evanorsouw/panelclock/doc/images/pcb_back.jpg

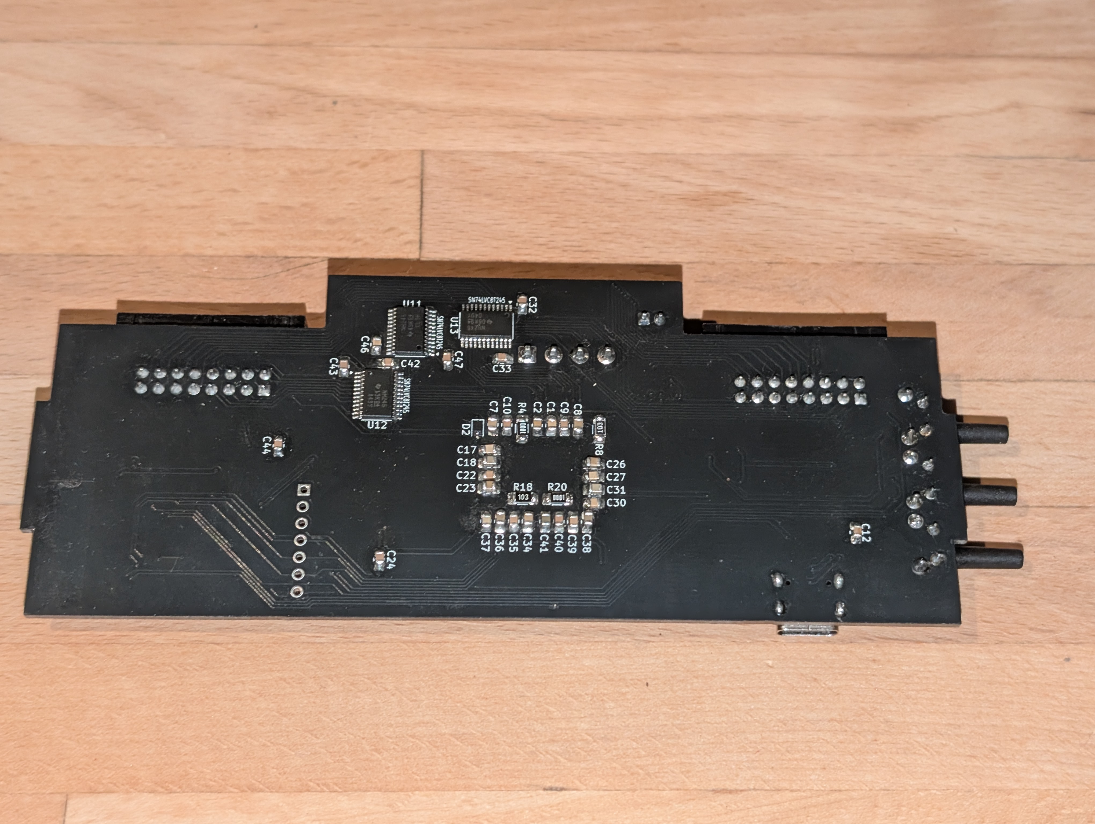
doc/images/pcb_back.jpg
