evanorsouw/panelclock/doc/images/parts_.jpg

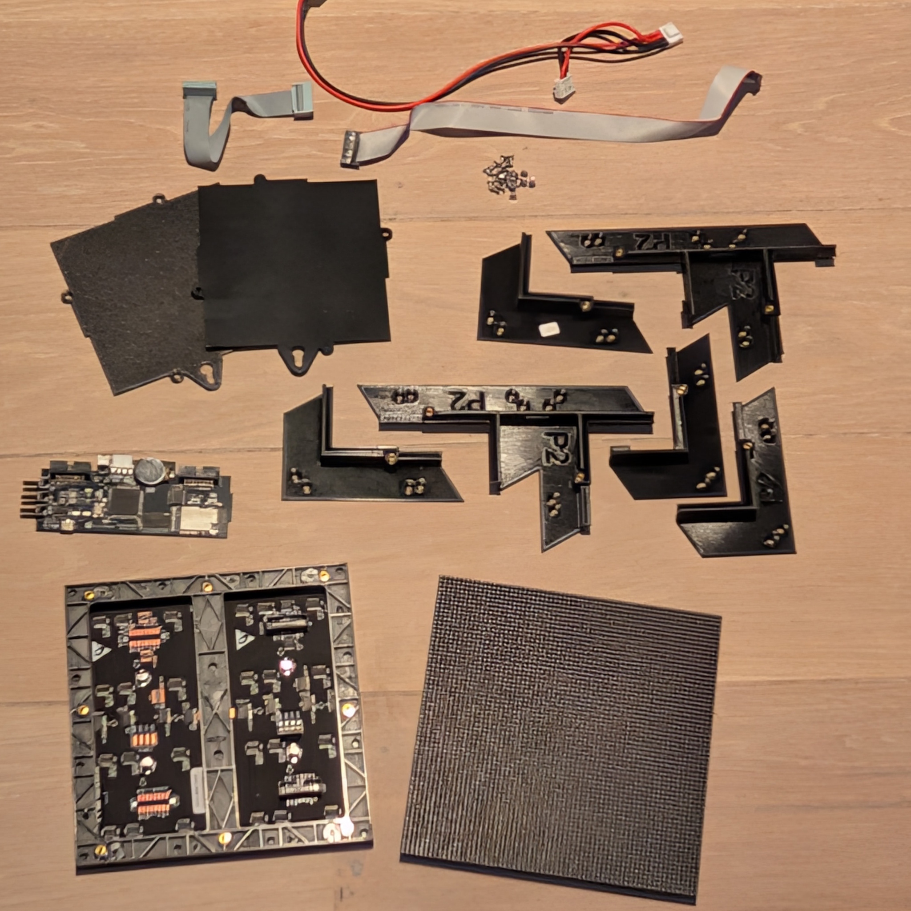
doc/images/parts_.jpg
