evanorsouw/panelclock/doc/images/partly_assembled.jpg

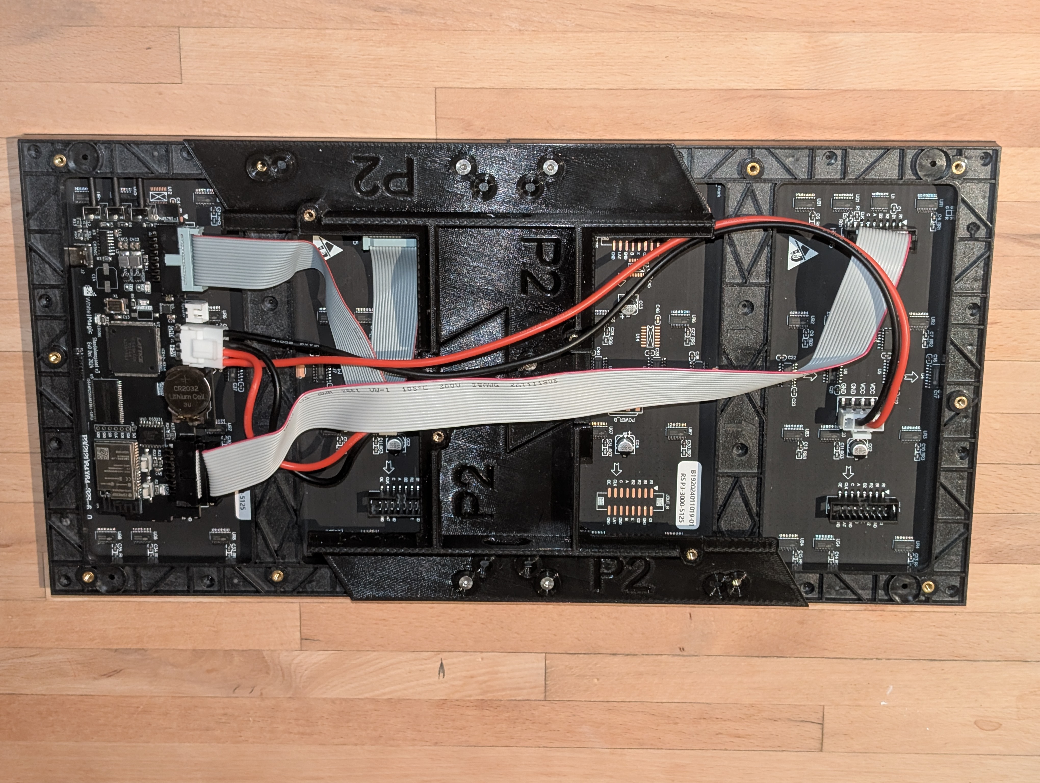
doc/images/partly_assembled.jpg
