evanorsouw/panelclock/electronics/kicad-fabrication-drill-options.png

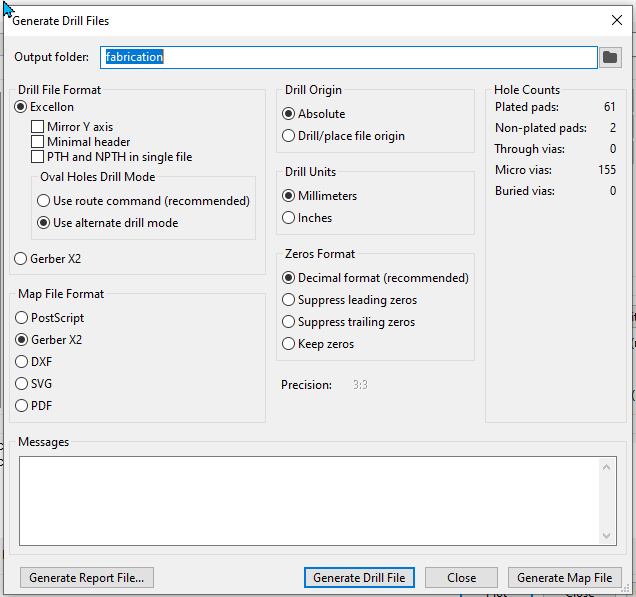
electronics/kicad-fabrication-drill-options.png
