evanorsouw/panelclock/electronics/kicad-fabrication-gerber-options.png

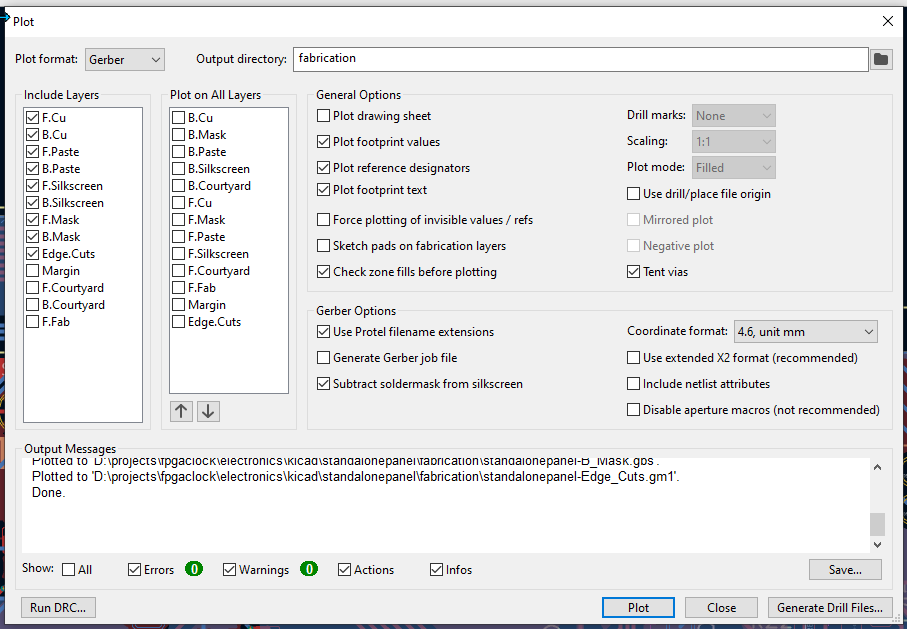
electronics/kicad-fabrication-gerber-options.png
