evanorsouw/panelclock/fpga/rtl/ledpanel_controller_tb.vhd

library IEEE;
use IEEE.STD_LOGIC_1164.all;
use IEEE.NUMERIC_STD.all;

entity ledpanel_controller_tb is
end entity ledpanel_controller_tb;

architecture Behavioral of ledpanel_controller_tb is
  
   component ledpanel_controller is
   port (    
      i_reset_n       : in std_logic;
      i_clk60M        : in std_logic;
      i_spi_clk       : in std_logic;
      i_spi_sdi       : in std_logic;
      --
      o_spi_sdo       : out std_logic;
      o_dsp_clk       : out std_logic;
      o_dsp_latch     : out std_logic;
      o_dsp_oe_n      : out std_logic;
      o_dsp_addr      : out std_logic_vector (4 downto 0);
      o_dsp_rgbs      : out std_logic_vector (11 downto 0);
      o_dsp_vbl       : out std_logic;
      -- sram pins
      o_sram_oe       : out std_logic;
      o_sram_wr       : out std_logic;
      o_sram_addr     : out std_logic_vector(17 downto 0);   -- 13 bits for 1 screen, use 17 for 16 screens
      o_sram_cs       : out std_logic;
      io_sram_data    : inout std_logic_vector(11 downto 0);
      --
      ot_test         : out std_logic
   );
   end component ledpanel_controller;

   constant CLOCK       : time := 1 sec / 48000000; -- 48MHz
   constant RAM_SPEED   : time := 10ns;
   constant BAUD        : time := 1 sec / 115200;

   -- module under test inputs
   signal tb_reset_n    : std_logic;
   signal tb_clk        : std_logic;
   signal tb_spi_clk    : std_logic;
   signal tb_spi_sdi    : std_logic;
   
   -- module under test outputs;
   signal tb_spi_sdo    : std_logic;
   signal tb_dsp_clk    : std_logic;
   signal tb_dsp_latch  : std_logic;
   signal tb_dsp_oe_n   : std_logic;
   signal tb_dsp_addr   : std_logic_vector (4 downto 0);
   signal tb_dsp_rgbs   : std_logic_vector (11 downto 0);
   signal tb_dsp_vbl    : std_logic;
   signal tb_sram_oe    : std_logic;
   signal tb_sram_wr    : std_logic;
   signal tb_sram_cs    : std_logic;
   signal tb_sram_addr  : std_logic_vector(17 downto 0);
   signal tb_sram_data  : std_logic_vector(11 downto 0);
   signal tb_test       : std_logic;
  
  type t_RAM is array (0 to 2**17-1) of std_logic_vector(11 downto 0);
  signal ram : t_RAM := (others => (others => '1'));
  
   begin
   MUT: ledpanel_controller
   port map (
      i_reset_n             => tb_reset_n,
      i_clk60M              => tb_clk,
      i_spi_clk             => tb_spi_clk,
      i_spi_sdi             => tb_spi_sdi,
                             
      o_spi_sdo             => tb_spi_sdo,
      o_dsp_clk             => tb_dsp_clk,
      o_dsp_latch           => tb_dsp_latch,
      o_dsp_oe_n            => tb_dsp_oe_n,
      o_dsp_addr            => tb_dsp_addr,
      o_dsp_rgbs            => tb_dsp_rgbs,
      o_dsp_vbl             => tb_dsp_vbl,
                       
      o_sram_oe             => tb_sram_oe,
      o_sram_cs             => tb_sram_cs,
      o_sram_wr             => tb_sram_wr,
      o_sram_addr           => tb_sram_addr,
      io_sram_data          => tb_sram_data,
      ot_test               => tb_test
   );
     
   tb_clk <= '0' after CLOCK / 2 when tb_clk = '1' else
             '1' after CLOCK / 2;

   p_ram : process(tb_sram_cs,tb_sram_wr,tb_sram_oe,tb_sram_addr,tb_sram_data)
   begin
      if tb_sram_cs = '1' then
         tb_sram_data <= (others => 'Z');
      elsif tb_sram_wr = '0' then 
         -- writing
         tb_sram_data <= (others => 'Z');
         ram(to_integer(unsigned(tb_sram_addr))) <= tb_sram_data;
      elsif tb_sram_oe = '1' then
         tb_sram_data <= (others => 'Z');
      else
         -- reading
         tb_sram_data <= ram(to_integer(unsigned(tb_sram_addr))) after RAM_SPEED;
      end if;
   end process;

   -- spi_stimulate : process
   -- variable v_byte : std_logic_vector(7 downto 0);
   -- begin
   
      -- tb_spi_clk <= '1';
      -- wait for 6 ms;

      -- tb_spi_clk <= '0';
      -- wait for 6 ms;

      -- tb_spi_sdo = '1';     

   -- end process spi_stimulate;
  
   reset_gen : process
   begin
      for i in 1 to 5 loop
         if (i < 4) then
            tb_reset_n <= '0';
         else
            tb_reset_n <= '1';
         end if;
         wait until falling_edge(tb_clk);
       end loop;
       wait on tb_reset_n;
   end process reset_gen;
   
end architecture Behavioral;
  
