evanorsouw/panelclock/sw/esp32/src/application.h

#ifndef _APPLICATION_H_
#define _APPLICATION_H_

#include <limits>
#include <memory>

#include "applicationcontext.h"
#include "bitmap.h"
#include "conwaylife.h"
#include "configurationui.h"
#include "ds3231.h"
#include "environment.h"
#include "graphics.h"
#include "renderbase.h"
#include "system.h"
#include "userinput.h"
#include "xy.h"

class Application : public RenderBase
{   
private:
    struct stripsegment 
    {
        /**
         * @brief calculate the required width of the segment in pixels.
         * @param graphics the graphics object targetting the segment with a width equal of the panel width.
         */
        std::function<int(Graphics &view)> width;  // calculate required segment width in pixels
        /**
         * @brief lambda to render the segment using th eprovided graphics object
         * @param graphics the graphics object targetting precisely the segment dimensions.
         * @param ox subpixel x-offset in range [0,1> to render to allow smooth scrolling
         */
        std::function<void(Graphics &graphics, float ox)> render;  // render the segment
    };

private:
    long _lasttime;
    float _weatherIntensity;
    std::vector<stripsegment> _stripSegments;
    int _iSegment;
    float _segmentOffset;
    std::shared_ptr<ConwayLife> _conway;

public:
    Application(ApplicationContext &appdata, IEnvironment &env, System &sys, UserInput &userinput);

    void init();
    void render(Graphics &graphics);
    int interact();
    
private:
    void drawSunRiseSet(Graphics& graphics, float x, float y, float diameter);
    void drawClock(Graphics& graphics, float x, float y, float diameter);
    void drawClockFlash(Graphics &graphics, float x, float y, float diameter);
    void drawTimeOnePanel(Graphics& graphics, const timeinfo &now);
    void drawDateTimeHorizontal(Graphics& graphics, const timeinfo &now);
    void drawDateTimeVertical(Graphics& graphics, const timeinfo &now);
    void drawWeatherOnePanel(Graphics& graphics);
    void drawWeatherHorizontal(Graphics& graphics);
    void drawWeatherVertical(Graphics& graphics);
    void drawWindArrow(Graphics& graphics, int x, int y, int size, float angle, Color col1, Color col2);
    void drawWeatherImage(Graphics& graphics);
    void drawWindAngle(Graphics& graphics);
    void drawLineFromCenter(Graphics& graphics, float x, float y, float diameter, float index, float l1, float l2, float thickness, Color color);
    void drawSun(Graphics& graphics, float x, float y, float width, float height, bool drawRays, const WeatherLayer &layer);
    fxy drawCloud(Graphics& graphics, float x, float y, float dx, float dy, const WeatherLayer &layer);
    void drawLightning(Graphics& graphics, float x, float y, const WeatherLayer &layer);
    void drawRain(Graphics& graphics, float x, float y, bool heavy, const WeatherLayer &layer);
    void drawHail(Graphics& graphics, float x, float y, const WeatherLayer &layer);
    void drawMoon(Graphics& graphics, float x, float y, float dx, float dy, const WeatherLayer &layer);
    void drawStars(Graphics& graphics, float x, float y, float dx, float dy, const WeatherLayer &layer);
    Color starIntensity(float phase, float when);
    void drawFog(Graphics& graphics, float x, float y, float dx, float dy, const WeatherLayer &layer);
    void drawSnow(Graphics& graphics, float x, float y, float dx, float dy, const WeatherLayer &layer);
    void drawHorizontalAnimatedLine(Graphics &graphics, float y);
    void drawBackgroundEffects(int mode, Graphics &graphics, const timeinfo &now);
    void runConwaysGameOfLife(int mode, Graphics &graphics, const timeinfo &now);

    void drawSegments(Graphics& graphics);
    stripsegment temperatureSegment();
    stripsegment windspeedSegment();
    stripsegment windangleSegment();
    stripsegment dateSegment();
    stripsegment separatorSegment();
    stripsegment colorSegment(int dx, Color color);

    Font *getSizedIconFont(char size, char defaultSize='L');
    Color scaleWeatherColor(Color color, Color defaultColor) { return scaleWeatherColor(color == Color::transparant ? defaultColor : color); }
    Color scaleWeatherColor(Color color) { return color * (_appctx.intensity() * _weatherIntensity); }        
};

#endif
