evanorsouw/panelclock/sw/esp32/src/bitmapfont.cpp

#include <algorithm>
#include <cstring>
#include <fcntl.h>
#include <string>
#include <sys/stat.h>
#include <unistd.h>
#include <esp_heap_caps.h>

#include "bitmapfont.h"
#include "utf8encoding.h"

#if 0
  #define LOG(...) printf(__VA_ARGS__)
#else
  #define LOG(...)
#endif

BitmapFont::~BitmapFont()
{
    heap_caps_free(_filedata);
    _filedata = nullptr;
    printf("unloaded font='%s' from memory\n", _fontname);
    delete _fontname;
}

BitmapFont *BitmapFont::getFont(const char *fontname)
{
    BitmapFont *font = nullptr;
    FILE *fp = nullptr;
    void *memory = nullptr;

    printf("loading font='%s'", fontname);
    do
    {
        auto path = std::string("/spiffs/") + fontname;
        struct stat info;
        if (stat(path.c_str(), &info) < 0)
        {
            printf(" - not found\n");
            break;
        }
        auto memory = heap_caps_malloc_prefer(info.st_size, 2, MALLOC_CAP_SPIRAM, MALLOC_CAP_DEFAULT);
        if (memory == nullptr)
        {
            printf(" - not enough memory\n");
            break;
        }
        fp = fopen(path.c_str(), "rb");
        if (fp == nullptr)
        {
            printf(" - cannot open\n");
            break;
        }
        auto n = fread(memory, 1, info.st_size, fp);
        if (n != info.st_size)
        {
            printf(" - failed to read all %ld bytes\n", info.st_size);
            break;
        }
        font = loadFont(fontname, memory, (int)info.st_size);

    } while (false);

    if (fp != nullptr)
    {
        fclose(fp);
    }
    if (font == nullptr && memory != nullptr)
    {
        free(memory);
    }
    printf("\n");
    return font;
}

int BitmapFont::splittext(const char *txt, float maxwidth) const
{
    auto dx = 0.0f;
    auto codepoint = 0;
    auto i = 0;
    auto ilast = 0;
    while ((codepoint = UTF8Encoding::nextCodepoint(txt, i)) != 0)
    {
        auto it = std::find_if(_glyphs.begin(), _glyphs.end(), [=](std::pair<uint16_t, glyphInfo*> kv) { return kv.first == (uint16_t)codepoint; });
        if (it != _glyphs.end())
        {
            auto nextdx = dx;
            if (nextdx > 0)
                nextdx += _info->tracking;
            nextdx += it->second->width;
            if (nextdx > maxwidth)
                break;
            dx = nextdx;
        }
        ilast = i;
    }
    return ilast;
}

textinfo BitmapFont::textsize(const char *txt) const
{
    auto codepoint = 0;
    auto i = 0;
    auto maxwidth = 0.0f;
    auto width = 0.0f;
    auto lines = 1;
    while ((codepoint = UTF8Encoding::nextCodepoint(txt, i)) != 0)
    {
        if (codepoint == '\n')
        {
            lines++;
            maxwidth = std::max(maxwidth, width);
            width = 0.0f;
        }
        else
        {
            auto it = std::find_if(_glyphs.begin(), _glyphs.end(), [=](std::pair<uint16_t, glyphInfo*> kv) { return kv.first == (uint16_t)codepoint; });
            if (it != _glyphs.end())
            {
                width += it->second->width;
                if (width > 0)
                    width += _info->tracking;
            }
        }
    }
    return textinfo(std::max(maxwidth, width), lines * height());
}

textinfo BitmapFont::charsize(int codepoint) const
{
    auto it = std::find_if(_glyphs.begin(), _glyphs.end(), [=](std::pair<uint16_t, glyphInfo*> kv) { return kv.first == (uint16_t)codepoint; });
    if (it == _glyphs.end())
        return textinfo();
    return textinfo(it->second->width, height());
}

BitmapFont *BitmapFont::loadFont(const char *fontname, void *filedata, int filesize)
{
    auto info = (bitmapfont*)filedata;
    fromBE(info->glyphcount);
    fromBE(info->offsetDescription);
    fromBE(info->offsetGlyphTable);
    
    if (info->version != 1)
    {
        printf(" - version='%d' not supported", info->version);
        return nullptr;
    }
    printf(" glyphcount='%d'", info->glyphcount);

    auto pglyph = (glyphInfo *)((uint8_t *)filedata + info->offsetGlyphTable);
    
    uint8_t maxWidth = 0;
    uint8_t maxHeight = 0;
    std::map<uint32_t, glyphInfo*> glyphs;
    for (int i=0; i<info->glyphcount; ++i)
    {
        fromBE(pglyph->unicode);
        glyphs[pglyph->unicode] = pglyph;
        maxWidth = std::max(maxWidth, pglyph->width);
        maxHeight = std::max(maxHeight, pglyph->height);
        auto size = sizeof(glyphInfo) + ((pglyph->width + 7) / 8) * pglyph->height - 1;
        LOG("-> '%c'/'%d' %d bytes\n", pglyph->unicode, pglyph->unicode, size);
        pglyph = (glyphInfo*)((uint8_t*)pglyph + size);
    }

    auto font = new BitmapFont();
    font->_fontname = fontname;
    font->_filedata = filedata;
    font->_info = info;
    font->_maxWidth = maxWidth;
    font->_maxHeight = maxHeight;
    font->_glyphs = std::move(glyphs);

    printf(" (size=%d, @%p)", filesize, filedata);

    return font;
}

void BitmapFont::fromBE(uint16_t &word)
{
    uint16_t bl = 0x1234;
    if (((uint8_t *)&bl)[0] == 0x34)
    {
        word = ((word & 0xFF) << 8) | ((word >> 8) & 0xFF);
    }
}

BitmapFont::glyphInfo* BitmapFont::getGlyph(uint32_t codepoint) const
{
    auto it = std::find_if(_glyphs.begin(), _glyphs.end(), [=](std::pair<uint16_t, glyphInfo *> kv) { return kv.first == codepoint; });
    if (it == _glyphs.end())
        return nullptr;
    return it->second;
}
