evanorsouw/panelclock/sw/esp32/src/version.cpp

#include "version.h"

// major.minor.buildno
// buildno is incremented with each build.
// major.minor must be updated manually.
#define VERSION "1.3.2486"

Version Version::application()
{
    return Version(VERSION);
}
