evanorsouw/panelclock/sw/esp32/src/timeinfo.h

#ifndef _TIMEINFO_H_
#define _TIMEINFO_H_

#include <time.h>
#include "translator.h"

#define TZ_CUSTOM "custom"

class  timeinfo
{
public:
    static const char *MonthsCompact[12];

private:
    const char *_weekdaysFull[7] = { ENG_MONDAY, ENG_TUESDAY, ENG_WEDNESDAY, ENG_THURSDAY, ENG_FRIDAY, ENG_SATURDAY, ENG_SUNDAY };
    const char *_weekdaysCompact[7] = { ENG_MON, ENG_TUE, ENG_WED, ENG_THU, ENG_FRI, ENG_SAT, ENG_SUN };
    const char *_monthsFull[12] = { ENG_JANUARY, ENG_FEBRUARY, ENG_MARCH, ENG_APRIL, ENG_MAY_LONG, ENG_JUNE, ENG_JULY, ENG_AUGUST, ENG_SEPTEMBER, ENG_OCTOBER, ENG_NOVEMBER, ENG_DECEMBER };
    static const int _daysInMonth[12];
    struct tm _tm;
    int _millies;
    int64_t _msticks;

public:
    timeinfo();
    timeinfo(const timeval &tv);

    int year() const { return 1900 + _tm.tm_year; }
    int mon() const { return _tm.tm_mon; }      // 0..11
    int yday() const { return _tm.tm_yday; }    // 0..365
    int mday() const { return _tm.tm_mday; }    // 1..31
    int wday() const { return (_tm.tm_wday + 6) % 7; }  // 0 = monday
    int hour() const { return _tm.tm_hour; }
    int min() const { return _tm.tm_min; }
    int sec() const { return _tm.tm_sec; }
    int millies() const { return _millies; }
    void millies(int value) { _millies = value % 1000; set(); }
    bool dst() const { return _tm.tm_isdst == 1; }
    /// @brief number of [m s] since epoch
    int64_t msticks() const { return _msticks; }    
    /// @brief number of [s] since epoch
    int64_t epoch() const { return _msticks / 1000; }    

    void setDate(int year, int month, int mday);
    void setTime(int hour, int minutes, int seconds);
    void hour(int value) { _tm.tm_hour = value % 24; set(); }
    void min(int value) { _tm.tm_min = value % 60; set(); }
    void sec(int value) { _tm.tm_sec = value % 60; set(); }
    void dst(bool dstActive) { _tm.tm_isdst = dstActive ? 1 : 0; }

    void addMinutes(int n) { set(n*60); }
    void addSeconds(int n) { set(n); }
    static int daysInMonth(int month, bool leapyear);

    const char *dayOfWeek(bool full=true) const { return full ? _weekdaysFull[wday()] : _weekdaysCompact[wday()]; }    
    const char *monthName(bool full=true) const { return full ? _monthsFull[mon()] : MonthsCompact[mon()] ; }    

    const struct tm *tm() const { return &_tm; } 

private:
    void set(time_t offsetSeconds = 0);
};

#endif
