evanorsouw/panelclock/sw/esp32/src/pixelsquare.h

#ifndef _PIXELSQUARE_H_
#define _PIXELSQUARE_H_

class PixelSquare 
{
protected:
    int _dx;
    int _dy;

public:
    PixelSquare(int dx, int dy) : _dx(dx), _dy(dy) {}
    virtual ~PixelSquare() {}

    int dx() const { return _dx; }
    int dy() const { return _dy; }
};

#endif
