evanorsouw/panelclock/sw/esp32/src/system.cpp

#include "system.h"

System::System(AppSettings *settings, DS3231 *rtc, Events *events) 
{
    _settings = settings;
    _rtc = rtc;
    _events = events;
    _wifiConnectedEvent = events->allocate("wificonnection");
    _wifi = nullptr;
    _translator = new Translator(settings->get(settings->KeyLanguage));
    startWifi();
}

System::~System()
{
    delete _translator;
    stopWifi();
}

void System::scanAPs()
{
    _wifi->scanAPs();
}

void System::connectWifi()
{
    if (!_wifi)
    {
        startWifi();
    }
    else
    {
        _wifi->connect(_settings->WifiSid().c_str(), _settings->WifiPassword().c_str());
    }
}

void System::disconnectWifi()
{
    stopWifi();
}

timeinfo System::now() const
{
    struct timeval tv;
    gettimeofday(&tv, nullptr);
    struct tm tm;
    localtime_r(&tv.tv_sec, &tm);
    return timeinfo(tv);
}

void System::now(const timeinfo &now)
{
    tod tod;
    tod.year = now.year();
    tod.mon = now.mon();
    tod.mday = now.mday();
    tod.wday = now.wday();
    tod.hour = now.hour();
    tod.min = now.min();
    tod.sec = now.sec();
    _rtc->setTime(&tod);
    
    struct timeval tv;
    tv.tv_sec = mktime((struct tm*)now.tm());
    tv.tv_usec = now.millies() * 1000;
    settimeofday(&tv, nullptr);
}

void System::startWifi()
{
    if (!_wifi)
    {
        _wifi = new WifiClient(_wifiConnectedEvent);
        connectWifi();
    }
}

void System::stopWifi()
{
    if (_wifi)
    {
        delete _wifi;
        _wifi = nullptr;
    }
}
