evanorsouw/panelclock/sw/esp32/src/timeinfo.cpp

#include "timeinfo.h"

const int timeinfo::_daysInMonth[12] = { 31,28,31,30,31,30,31,31,30,31,30,31 };
const char *timeinfo::MonthsCompact[12] = { ENG_JAN, ENG_FEB, ENG_MAR, ENG_APR, ENG_MAY_SHORT, ENG_JUN, ENG_JUL, ENG_AUG, ENG_SEP, ENG_OCT, ENG_NOV, ENG_DEC };

timeinfo::timeinfo() 
{
    _tm.tm_year = 70;
    _tm.tm_mon = 0;
    _tm.tm_mday = 1;
    _tm.tm_yday = 0;
    _tm.tm_wday = 0;
    _tm.tm_hour = 0;
    _tm.tm_min = 0;
    _tm.tm_sec = 0;
    _tm.tm_isdst = -1;
    _millies = 0;
    _msticks = 0;
}

timeinfo::timeinfo(const timeval &tv)
{
    localtime_r(&tv.tv_sec, &_tm);
    _tm.tm_isdst = -1;
    _millies = tv.tv_usec / 1000;
    _msticks = (tv.tv_sec * 1000000 + tv.tv_usec) / 1000;
}

void timeinfo::setDate(int year, int month, int mday)
{
    _tm.tm_year = year - 1900;
    _tm.tm_mon = month;
    _tm.tm_mday = mday;
    set();
}

void timeinfo::setTime(int hours, int minutes, int seconds)
{
    _tm.tm_hour = hours;
    _tm.tm_min = minutes;
    _tm.tm_sec = seconds;
    _millies = 0;
    set();
}

int timeinfo::daysInMonth(int month, bool leapyear)
{
    if (month < 0 || month > 11)
        return 0;
    return _daysInMonth[month] + ((month == 1 && leapyear) ? 1 : 0); 
}

void timeinfo::set(time_t offsetSeconds)
{
    auto secs = mktime(&_tm) + offsetSeconds;
    localtime_r(&secs, &_tm);
    _msticks = secs * 1000 + _millies;
}
