evanorsouw/panelclock/sw/esp32/src/spiwrapper.h

#ifndef SPIWRAPPER_H_
#define SPIWRAPPER_H_

#include "driver/gpio.h"
#include "esp_spiffs.h"
#include "driver/spi_master.h"

class SpiWrapper
{
private:
    spi_host_device_t _host;
    gpio_num_t _clk;
    gpio_num_t _mosi;
    gpio_num_t _miso;
    spi_device_handle_t _hspi;
    int _speed;
    int _mode;
    bool _fullduplex;
    bool _initialized;

public:
    SpiWrapper(spi_host_device_t host, gpio_num_t clk, gpio_num_t mosi, gpio_num_t miso, int speed, bool fullduplex)
    {
        _host = host;
        _clk = clk;
        _mosi = mosi;
        _miso = miso;
        _speed = speed;
        _fullduplex = fullduplex;
        _mode = 0;  // spi mode 0 (rising edge
        _initialized = false;
    }

    virtual ~SpiWrapper() 
    {
        end();
    }

    void start()
    {
        if (_initialized)
        {
            end();            
        }
        gpio_set_direction(_clk, GPIO_MODE_OUTPUT);
        gpio_set_direction(_mosi, GPIO_MODE_OUTPUT);
        gpio_set_direction(_miso, GPIO_MODE_INPUT);

        spi_bus_config_t bus_config = {0};
        bus_config.mosi_io_num = _mosi;
        bus_config.miso_io_num = _miso;
        bus_config.sclk_io_num = _clk;
        bus_config.quadwp_io_num = -1;
        bus_config.quadhd_io_num = -1;
        bus_config.max_transfer_sz = 3;

        ESP_ERROR_CHECK(spi_bus_initialize(_host, &bus_config, SPI_DMA_CH_AUTO));

        spi_device_interface_config_t devcfg = {0};
        devcfg.mode = _mode;
        devcfg.clock_speed_hz = _speed;
        devcfg.spics_io_num = -1;     
        devcfg.flags = (_fullduplex ? 0 : SPI_DEVICE_HALFDUPLEX);
        devcfg.queue_size = 1;
        devcfg.pre_cb = NULL;
        devcfg.post_cb = NULL;

        ESP_ERROR_CHECK(spi_bus_add_device(_host, &devcfg, &_hspi));

        _initialized = true;

        printf("intialized SPI bus=%d %s-duplex, mode=%d, mosi=%d, miso=%d, clk=%d, speed=%d\n", 
            _host, _fullduplex ? "full" : "half", _mode, _mosi, _miso, _clk, _speed);
    }

    void end()
    {
        if (_initialized)
        {
            ESP_ERROR_CHECK(spi_bus_remove_device(_hspi));
            ESP_ERROR_CHECK(spi_bus_free(_host));
            _initialized = false;
            printf("terminated SPI bus=%d\n", _host);
        }
    }

    void write(uint8_t *buf, int n)
    {
        spi_transaction_t t = {
            .length = (size_t)(n * 8),
            .tx_buffer = buf
        };

        ESP_ERROR_CHECK(spi_device_polling_transmit(_hspi, &t));
    }

    void transfer(uint8_t *wbuf, int nw, uint8_t *rbuf, int nr)
    {
        spi_transaction_t t = {
            .length = (size_t)(nw * 8),
            .rxlength = (size_t)(nr * 8),
            .tx_buffer = wbuf,
            .rx_buffer = rbuf
        };

        ESP_ERROR_CHECK(spi_device_polling_transmit(_hspi, &t));
    }
};

#endif
